Kyuubi0323/Bachelor_Project/Firmware_Reference/sc_app/simcom_lib/inc/simcom_A7600C1_V4_01_gpio.h

/**
  ******************************************************************************
  * @file    simcom_A7600C1_V4_01_gpio.h
  * @author  SIMCom OpenSDK Team
  * @brief   Header file of A7600C1 V4 01 GPIO configuration, please refer to related HD description.
  ******************************************************************************
  * @attention
  *
  * Copyright (c) 2022 SIMCom Wireless.
  * All rights reserved.
  *
  ******************************************************************************
  */
#ifndef __SIMCOM_A7600C1_V4_01_GPIO_H__
#define __SIMCOM_A7600C1_V4_01_GPIO_H__

typedef enum
{
    SC_MODULE_GPIO_0 = 0,
    SC_MODULE_GPIO_1 = 1,
    SC_MODULE_GPIO_2 = 2,
    SC_MODULE_GPIO_3 = 3,
    SC_MODULE_GPIO_4 = 4,
    SC_MODULE_GPIO_5 = 5,
    SC_MODULE_GPIO_6 = 6,
    SC_MODULE_GPIO_7 = 7,
    SC_MODULE_GPIO_8 = 8,
    SC_MODULE_GPIO_9 = 9,
    SC_MODULE_GPIO_10 = 10,
    SC_MODULE_GPIO_11 = 11,
    SC_MODULE_GPIO_12 = 12,
    SC_MODULE_GPIO_13 = 13,
    SC_MODULE_GPIO_14 = 14,
    SC_MODULE_GPIO_15 = 15,
    SC_MODULE_GPIO_16 = 16,
    SC_MODULE_GPIO_17 = 17,
    SC_MODULE_GPIO_18 = 18,
    SC_MODULE_GPIO_19 = 19,
    SC_MODULE_GPIO_20 = 20,
    SC_MODULE_GPIO_21 = 21,
    SC_MODULE_GPIO_22 = 22,
    SC_MODULE_GPIO_23 = 23,
    SC_MODULE_GPIO_24 = 24,
    SC_MODULE_GPIO_25 = 25,
    SC_MODULE_GPIO_MAX
}SC_Module_GPIONumbers;


#endif
