Kyuubi0323/Bachelor_Project/Firmware_Reference/sc_app/simcom_lib/inc/simcom_A7630C_LAAL_gpio.h

/**
  ******************************************************************************
  * @file    simcom_A7630C_LAAL_gpio.h
  * @author  SIMCom OpenSDK Team
  * @brief   Header file of A7630C LAAL GPIO configuration, please refer to related HD description.
  ******************************************************************************
  * @attention
  *
  * Copyright (c) 2022 SIMCom Wireless.
  * All rights reserved.
  *
  ******************************************************************************
  */
#ifndef __SIMCOM_A7670C_LAAL_GPIO_H__
#define __SIMCOM_A7670C_LAAL_GPIO_H__

typedef enum
{
    SC_MODULE_GPIO_4 = 4,
    SC_MODULE_GPIO_5 = 5,
    SC_MODULE_GPIO_6 = 6,
    SC_MODULE_GPIO_7 = 7,
    SC_MODULE_GPIO_8 = 8,
    SC_MODULE_GPIO_9 = 9,
    SC_MODULE_GPIO_10 = 10,
    SC_MODULE_GPIO_12 = 12,
    SC_MODULE_GPIO_13 = 13,
    SC_MODULE_GPIO_14 = 14,
    SC_MODULE_GPIO_15 = 15,
    SC_MODULE_GPIO_16 = 16,
    SC_MODULE_GPIO_17 = 17,
    SC_MODULE_GPIO_19 = 19,
    SC_MODULE_GPIO_20 = 20,
    SC_MODULE_GPIO_25 = 25,
    SC_MODULE_GPIO_26 = 26,
    SC_MODULE_GPIO_27 = 27,
    SC_MODULE_GPIO_28 = 28,
    SC_MODULE_GPIO_29 = 29,
    SC_MODULE_GPIO_30 = 30,
    SC_MODULE_GPIO_31 = 31,
    SC_MODULE_GPIO_32 = 32,
    SC_MODULE_GPIO_33 = 33,
    SC_MODULE_GPIO_34 = 34,
    SC_MODULE_GPIO_MAX

}SC_Module_GPIONumbers;
#endif
