Kyuubi0323/Bachelor_Project/Firmware_Reference/sc_app/simcom_demo/demo_network.c

/**
  ******************************************************************************
  * @file    demo_network.c
  * @author  SIMCom OpenSDK Team
  * @brief   Source file of network management.
  ******************************************************************************
  * @attention
  *
  * Copyright (c) 2022 SIMCom Wireless.
  * All rights reserved.
  *
  ******************************************************************************
  */

/* Includes ------------------------------------------------------------------*/
#include "simcom_api.h"
#include "stdlib.h"
#include "string.h"
#include "stdio.h"

#if 0
static sTaskRef networkTaskRef;
static unsigned char *networkTaskStack = NULL;
#endif

sTimerRef networkTimerRef;
extern sMsgQRef simcomUI_msgq;
extern void PrintfOptionMenu(INT8* options_list[], int array_size);
extern void PrintfResp(INT8* format);

typedef struct{
    int cid;
    char pdptype[20];
    char apn[20];
}SCcgdcontParm;
typedef struct{
    int mode;
    int format;
    char oper[20];
    int act;
}SCcopsParm;

#if 0
static void sTask_NetWork(void *arg)
{
    SC_STATUS status;
    SIM_MSG_T cmmsg;

    int ret = 0;
    unsigned int loop=0;

    while(loop++ < 100)
    {
        unsigned char csq;
        unsigned char ret;
        SCcpsiParm Scpsi;
        char cops[100]={0};
        char cpin[50]={0};
        char cgdcont[500]={0};
        char cgact[200]={0};
        int creg,cgreg,cnmp,cgatt;
        char iccid[32] = {0};
        int cfun = 0;
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
